TomWhitwell/TH-VCO1/Collateral/340-3094-3906.jpg

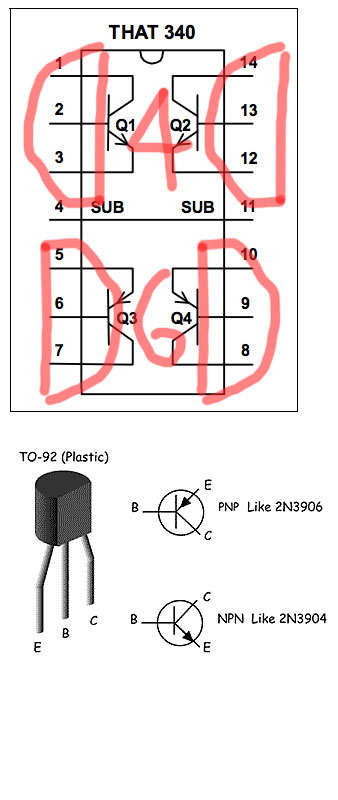
Collateral/340-3094-3906.jpg
